BradleyConn/lawn-rover/cad/stl/esp32_lid_v1.stl

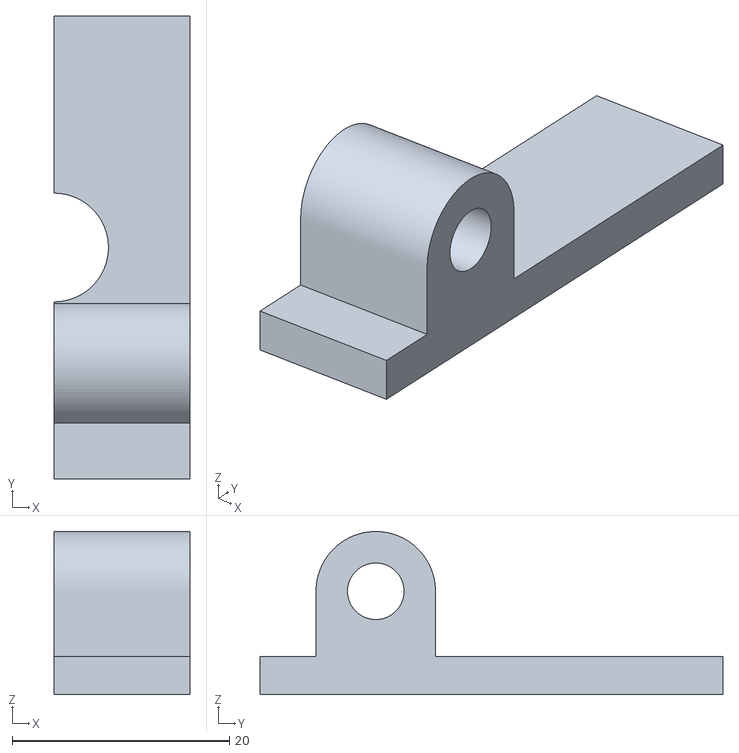
[picture p19: CAD file, 2023-04-28]
cad/stl/esp32_lid_v1.stl
12.5 x 42.6 x 15.0
