BradleyConn/lawn-rover/cad/stl/mount_insert.stl

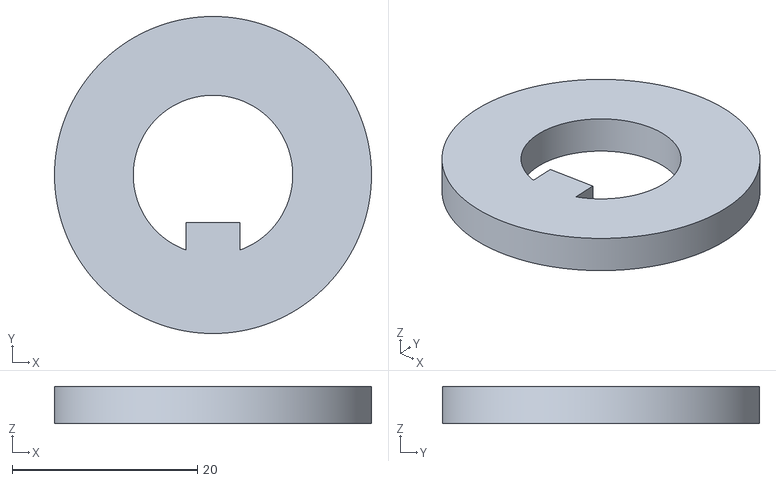
[picture p20: CAD file, 2023-04-28]
cad/stl/mount_insert.stl
34.2 x 34.2 x 4.00
